Rafaelk1006/Baton-guiador-con-deteccion/Diagramas/Esquema planteado.jpg

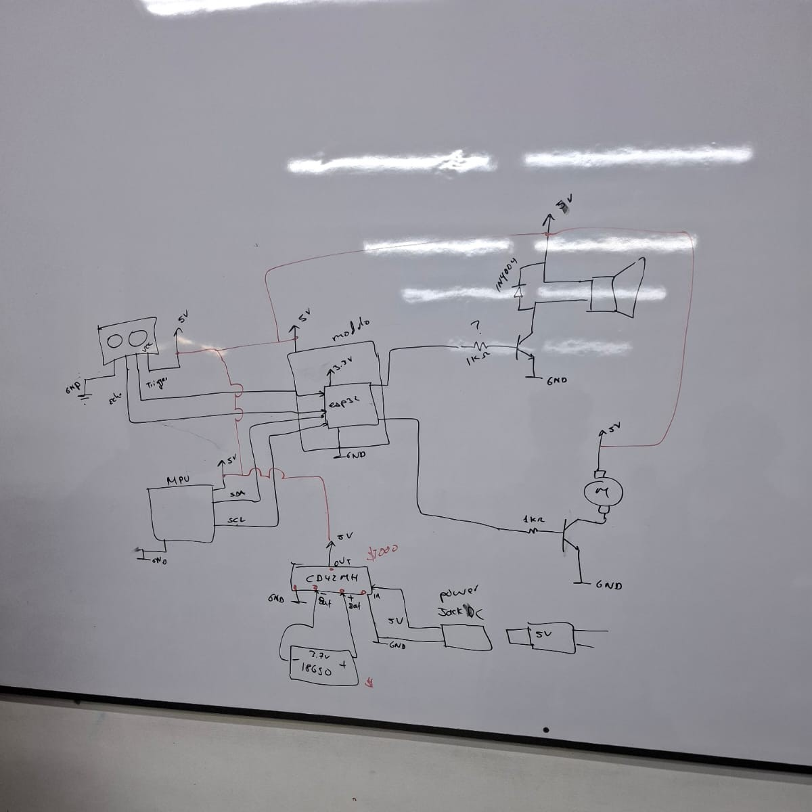
Diagramas/Esquema planteado.jpg
