Rafaelk1006/Baton-guiador-con-deteccion/Evidencias/Cable.jpg

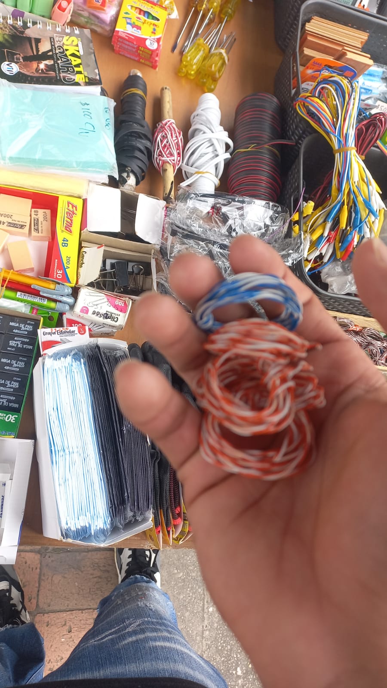
Evidencias/Cable.jpg
