Rafaelk1006/Baton-guiador-con-deteccion/Evidencias/Evidencia de trabajo.jpg

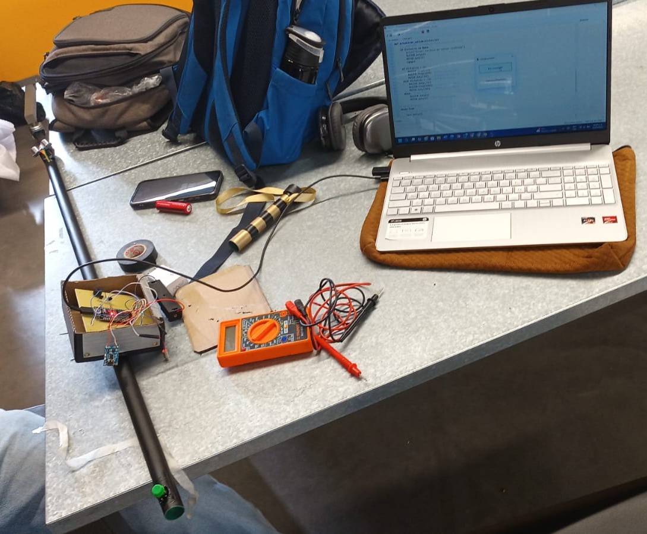
Evidencias/Evidencia de trabajo.jpg
