Rafaelk1006/Baton-guiador-con-deteccion/Evidencias/Implementación 2.jpg

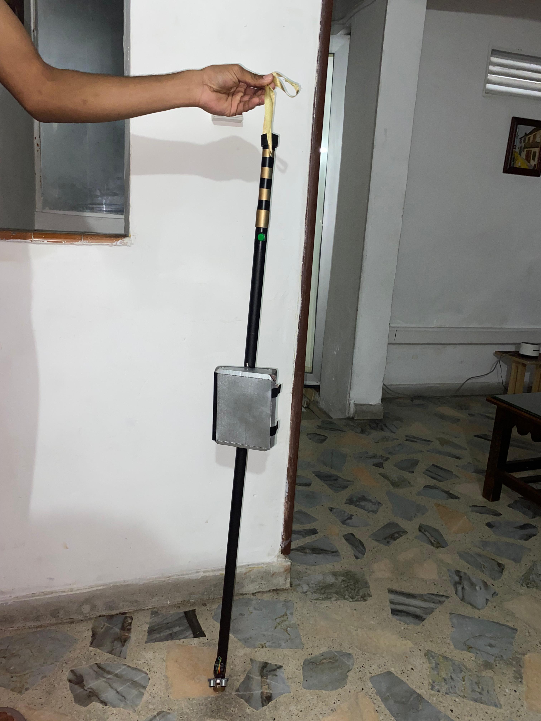
Evidencias/Implementación 2.jpg
