Rafaelk1006/Baton-guiador-con-deteccion/Evidencias/Implementación 3.jpg

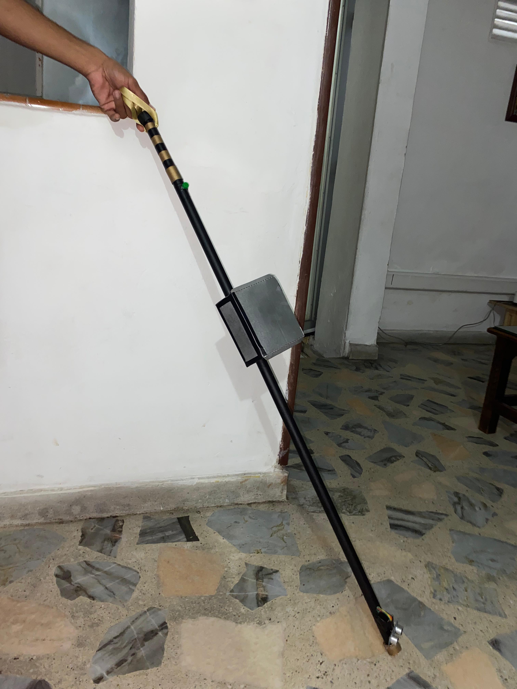
Evidencias/Implementación 3.jpg
