Rafaelk1006/Baton-guiador-con-deteccion/Evidencias/Implementación 4.jpg

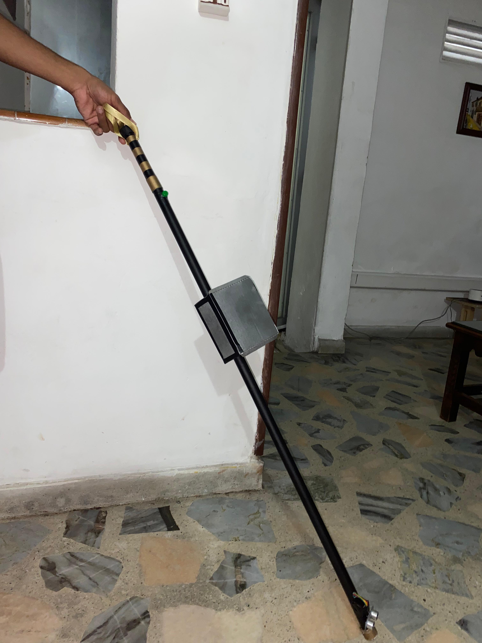
Evidencias/Implementación 4.jpg
