Rafaelk1006/Baton-guiador-con-deteccion/Evidencias/Implementación.jpg

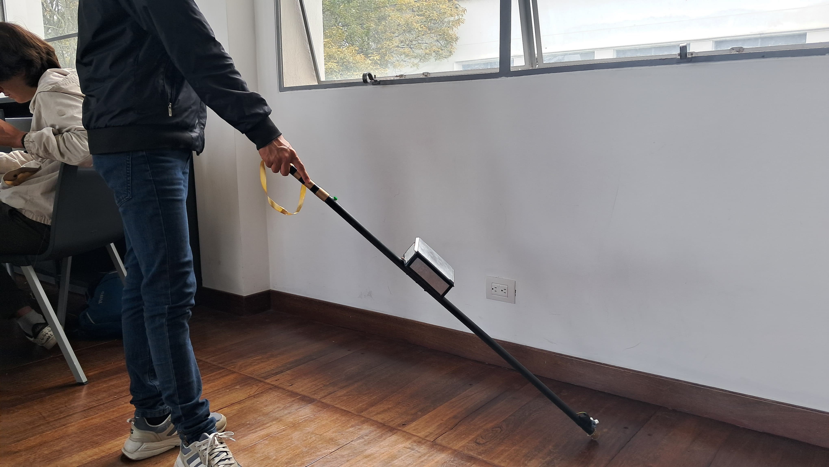
Evidencias/Implementación.jpg
