Rafaelk1006/Baton-guiador-con-deteccion/Evidencias/Pcb.jpg

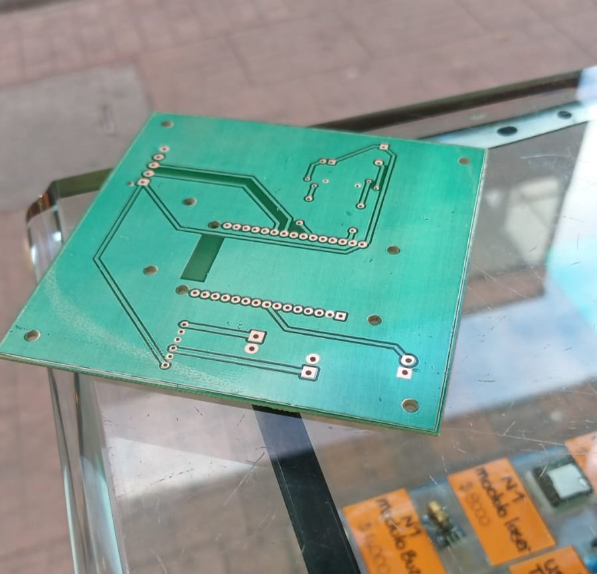
Evidencias/Pcb.jpg
