Rafaelk1006/Baton-guiador-con-deteccion/PCB/Soldadura.jpg

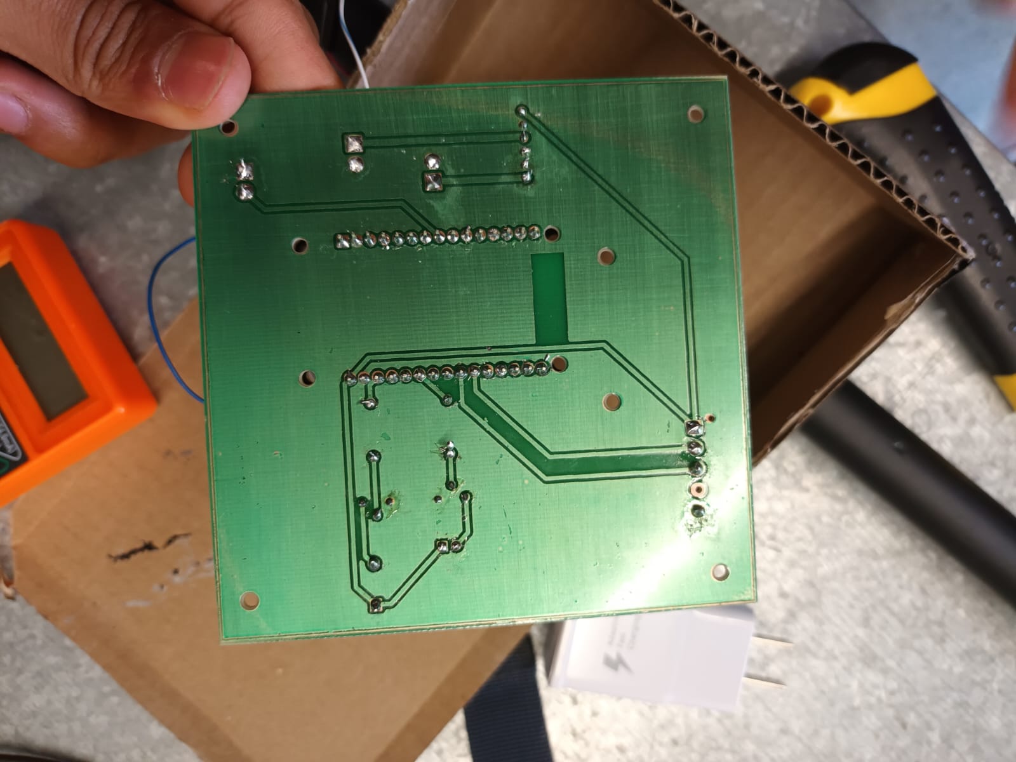
PCB/Soldadura.jpg
