Rafaelk1006/Baton-guiador-con-deteccion/PCB/Vista 3D otra cara.png

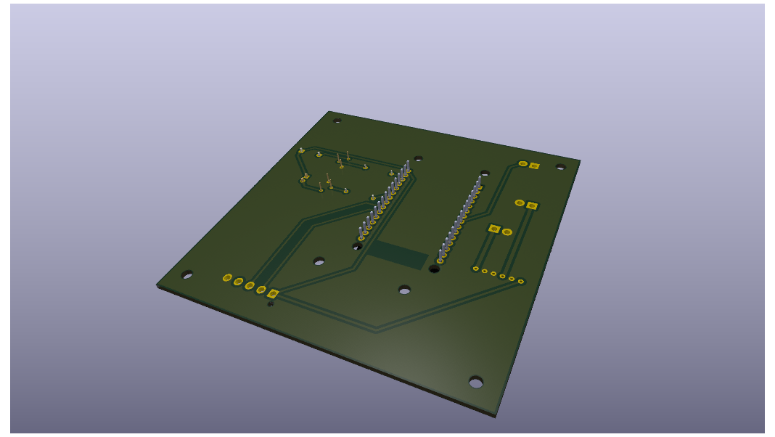
PCB/Vista 3D otra cara.png
