Rafaelk1006/Baton-guiador-con-deteccion/Evidencias/Componentes.jpg

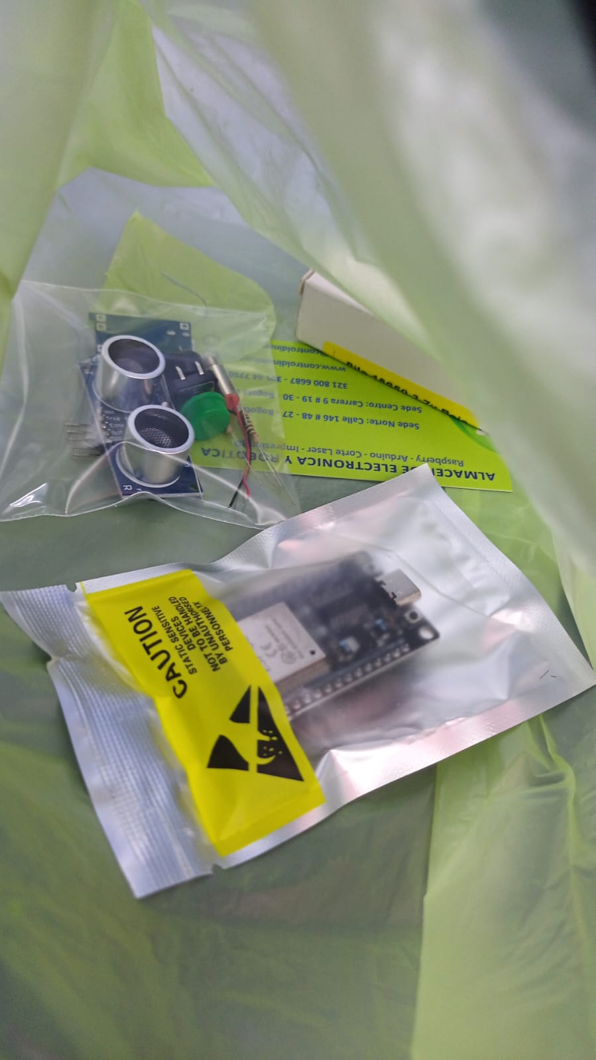
Evidencias/Componentes.jpg
