Rafaelk1006/Baton-guiador-con-deteccion/PCB/Componentes interconectados.jpg

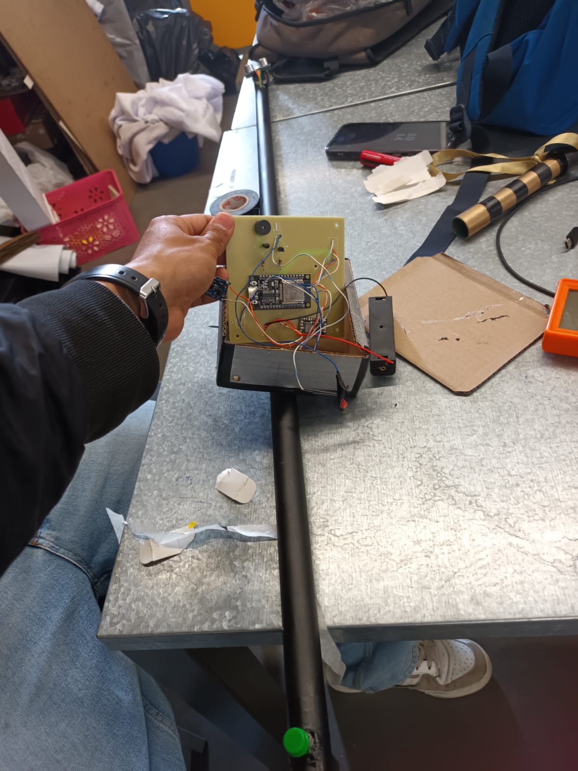
PCB/Componentes interconectados.jpg
