Rafaelk1006/Baton-guiador-con-deteccion/PCB/Fotografia PCB fabricada 2.jpg

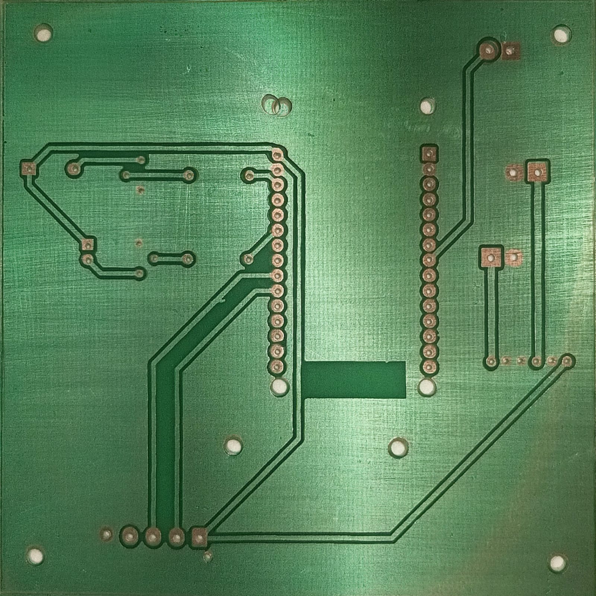
PCB/Fotografia PCB fabricada 2.jpg
