Rafaelk1006/Baton-guiador-con-deteccion/Evidencias/Todo junto.png

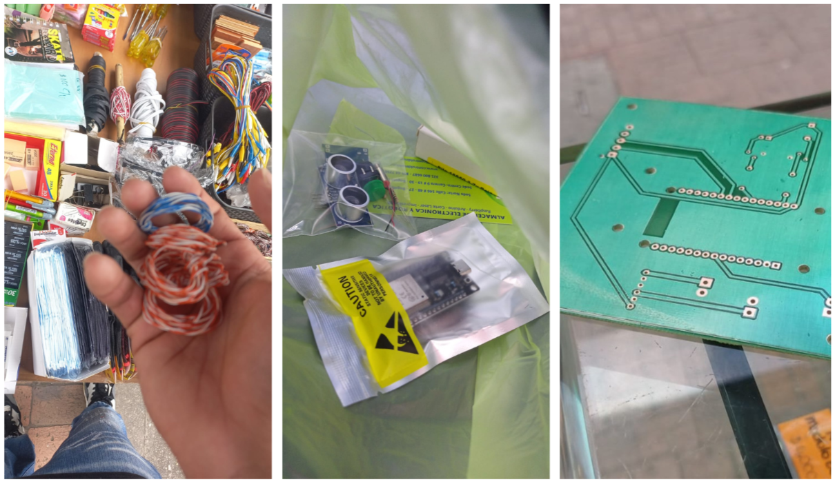
Evidencias/Todo junto.png
